Apollo-Simulation-Peripheral-Lab/DSKY/3D Models/iPhone 13 Version/Cover (iPhone 13).3mf

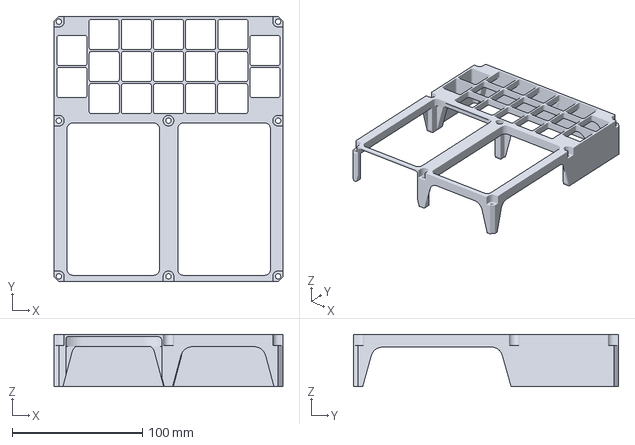
[picture p16: CAD file, 2024-06-18]
3D Models/iPhone 13 Version/Cover (iPhone 13).3mf
175.3 x 203.2 x 39.9 mm
