Apollo-Simulation-Peripheral-Lab/DSKY/3D Models/Common Models/Alarm Housing Top.stl

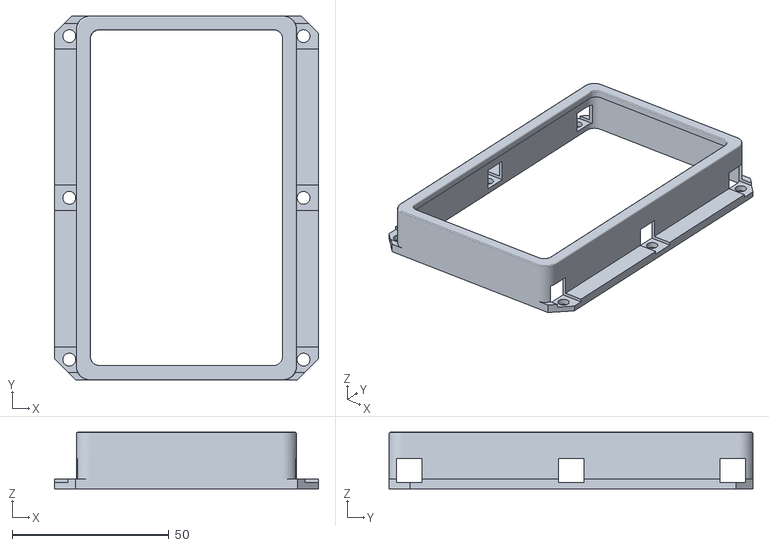
[picture p17: CAD file, 2024-06-30]
3D Models/Common Models/Alarm Housing Top.stl
84.2 x 116.1 x 18.0
