Apollo-Simulation-Peripheral-Lab/DSKY/3D Models/HDMI Version/Display Housing (HDMI).stl

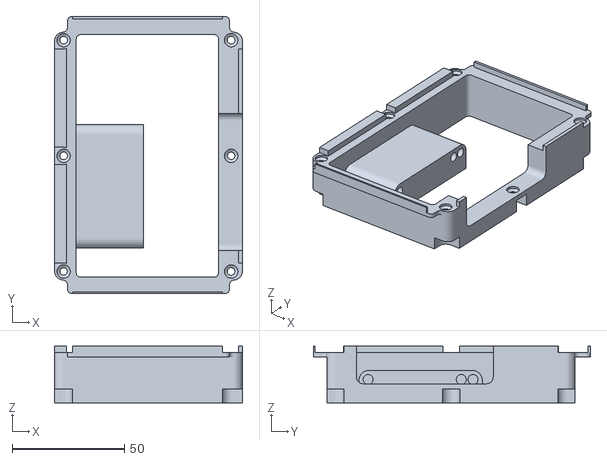
[picture p18: CAD file, 2024-06-30]
3D Models/HDMI Version/Display Housing (HDMI).stl
83.8 x 123.5 x 25.3
