Apollo-Simulation-Peripheral-Lab/DSKY/3D Models/iPhone 12 Mini Version/Frame (iPhone 12 Mini).3mf

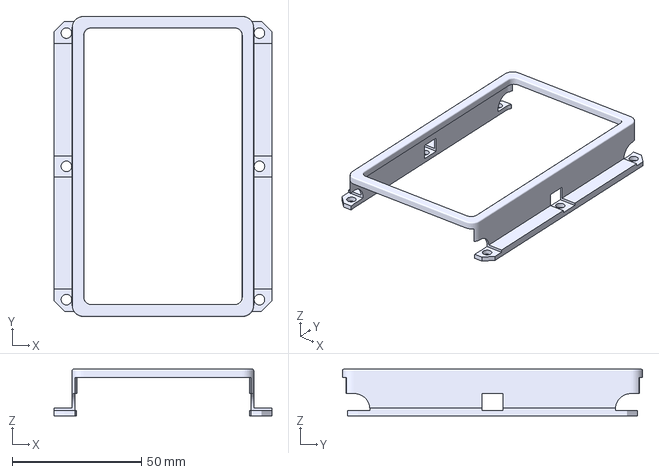
[picture p19: CAD file, 2024-06-18]
3D Models/iPhone 12 Mini Version/Frame (iPhone 12 Mini).3mf
84.2 x 116.1 x 18.0 mm
