Apollo-Simulation-Peripheral-Lab/DSKY/3D Models/Common Models/Keyboard Holder.stl

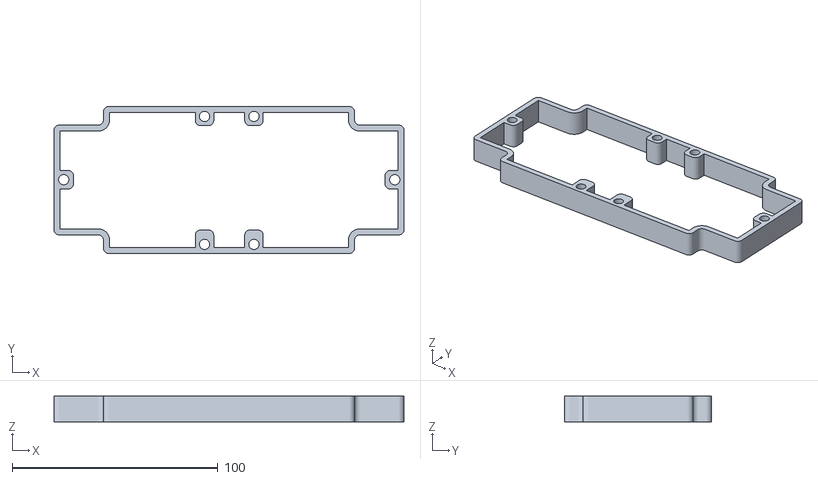
[picture p20: CAD file, 2024-06-30]
3D Models/Common Models/Keyboard Holder.stl
170.0 x 71.4 x 12.4
