Apollo-Simulation-Peripheral-Lab/DSKY/3D Models/HDMI Version/Compact Enclosure.stl

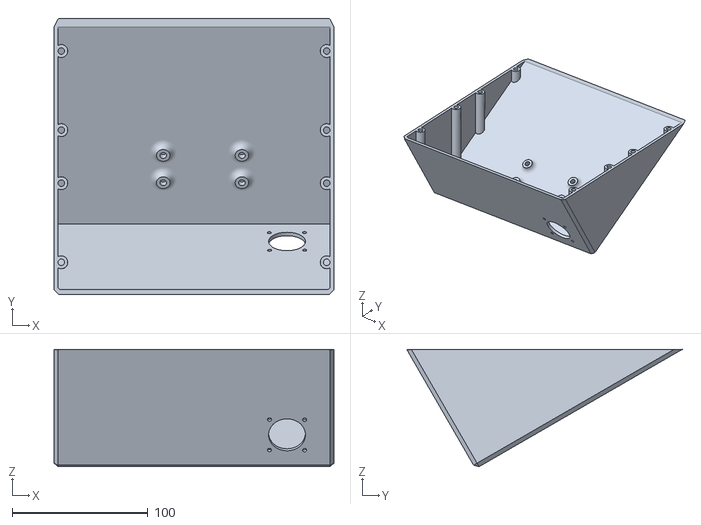
[picture p21: CAD file, 2024-06-30]
3D Models/HDMI Version/Compact Enclosure.stl
206.3 x 203.2 x 86.5
