Apollo-Simulation-Peripheral-Lab/DSKY/3D Models/Common Models/Alarm Housing Bottom.stl

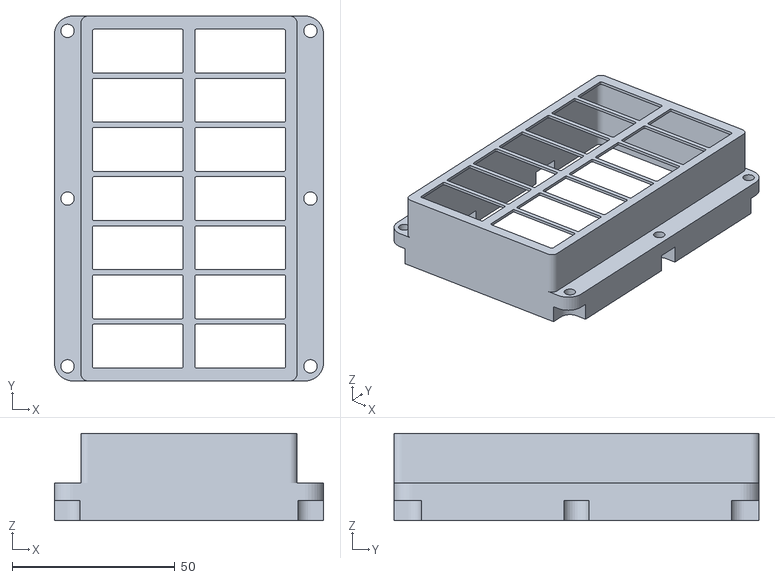
[picture p22: CAD file, 2024-06-30]
3D Models/Common Models/Alarm Housing Bottom.stl
82.8 x 112.2 x 26.9
