Apollo-Simulation-Peripheral-Lab/DSKY/3D Models/Common Models/Mount Top.stl

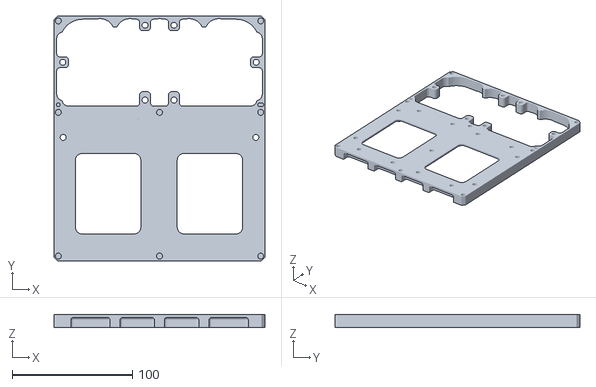
[picture p23: CAD file, 2024-06-18]
3D Models/Common Models/Mount Top.stl
175.3 x 203.2 x 10.9
