Apollo-Simulation-Peripheral-Lab/DSKY/3D Models/HDMI Version/Enclosure middle.3mf

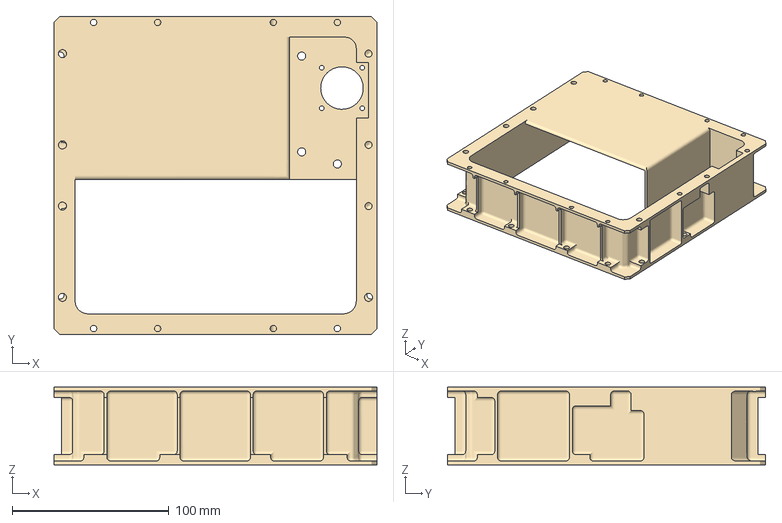
[picture p24: CAD file, 2024-04-06]
3D Models/HDMI Version/Enclosure middle.3mf
206.3 x 203.2 x 49.8 mm
