Apollo-Simulation-Peripheral-Lab/DSKY/3D Models/Common Models/Keys/KEY REL.stl

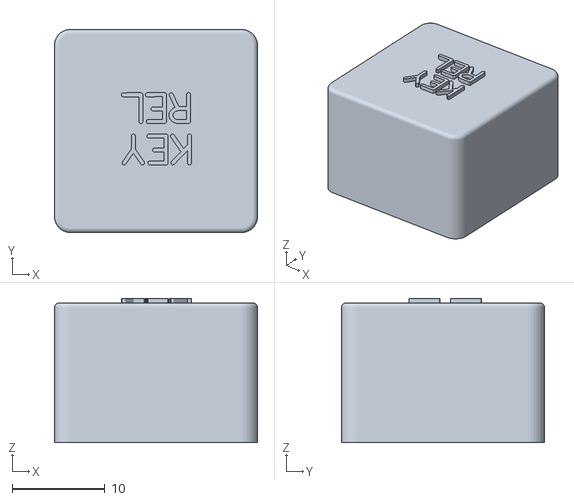
[picture p25: CAD file, 2024-06-18]
3D Models/Common Models/Keys/KEY REL.stl
21.8 x 21.8 x 15.5
