Apollo-Simulation-Peripheral-Lab/DSKY/3D Models/Common Models/Mount Bottom.stl

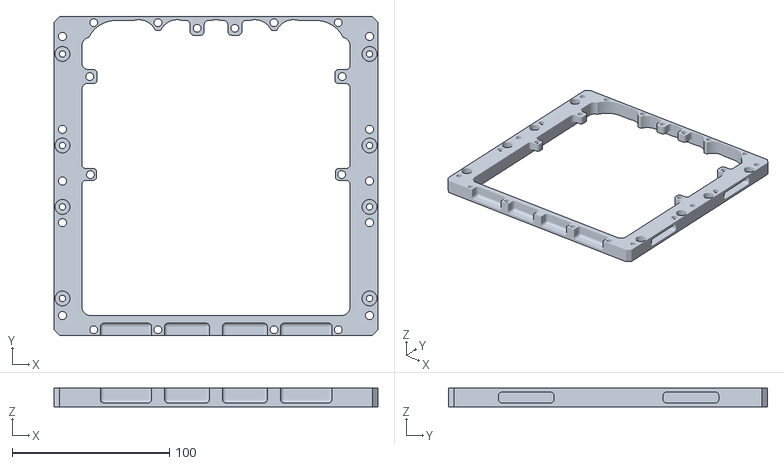
[picture p26: CAD file, 2024-06-18]
3D Models/Common Models/Mount Bottom.stl
206.3 x 203.2 x 12.0
