Apollo-Simulation-Peripheral-Lab/DSKY/3D Models/HDMI Version/Enclosure bottom.3mf

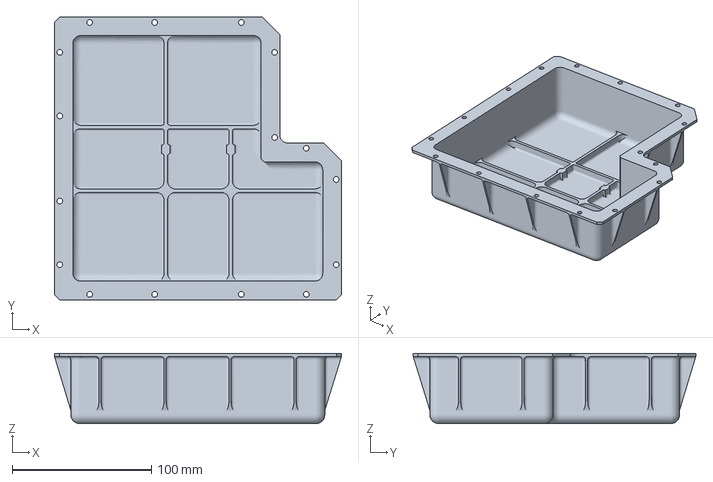
[picture p27: CAD file, 2024-02-14]
3D Models/HDMI Version/Enclosure bottom.3mf
206.3 x 203.2 x 50.4 mm
