Apollo-Simulation-Peripheral-Lab/DSKY/3D Models/Common Models/Enclosure middle (top half).3mf

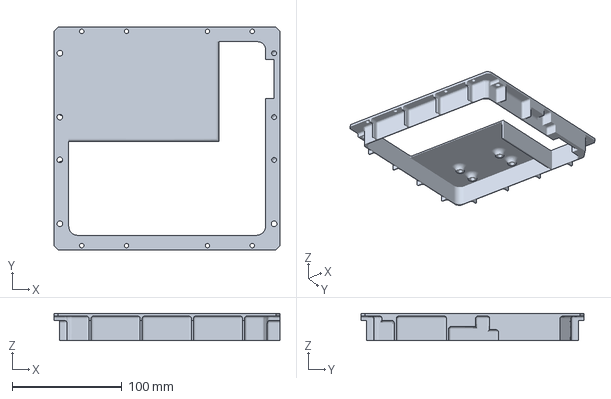
[picture p28: CAD file, 2024-06-18]
3D Models/Common Models/Enclosure middle (top half).3mf
206.3 x 203.2 x 25.0 mm
