Apollo-Simulation-Peripheral-Lab/DSKY/3D Models/Common Models/Alarm Splitter.3mf

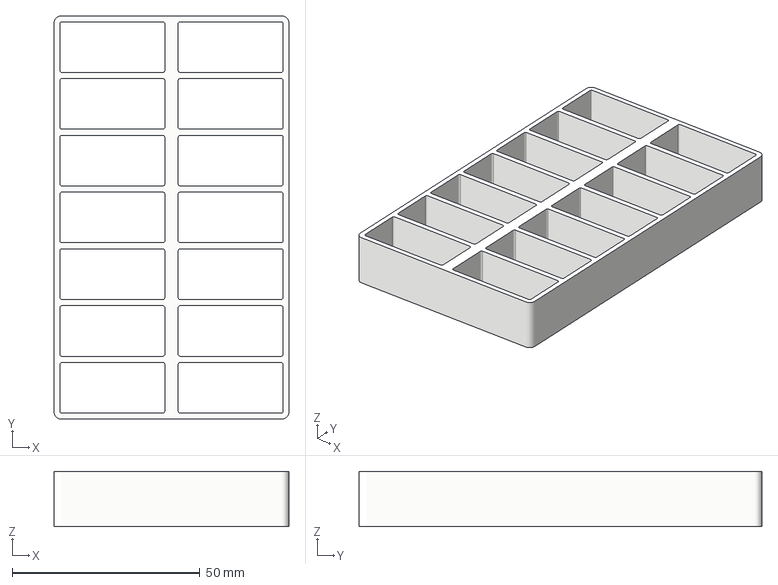
[picture p29: CAD file, 2024-06-18]
3D Models/Common Models/Alarm Splitter.3mf
62.5 x 107.3 x 14.7 mm
