Apollo-Simulation-Peripheral-Lab/DSKY/3D Models/Common Models/Enclosure middle (bottom half).3mf

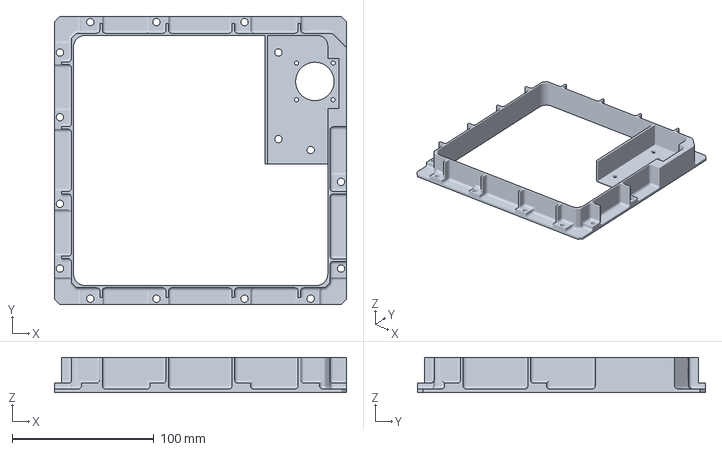
[picture p30: CAD file, 2024-06-18]
3D Models/Common Models/Enclosure middle (bottom half).3mf
206.3 x 203.2 x 24.8 mm
