Apollo-Simulation-Peripheral-Lab/DSKY/3D Models/Common Models/Mount (single print discouraged).3mf

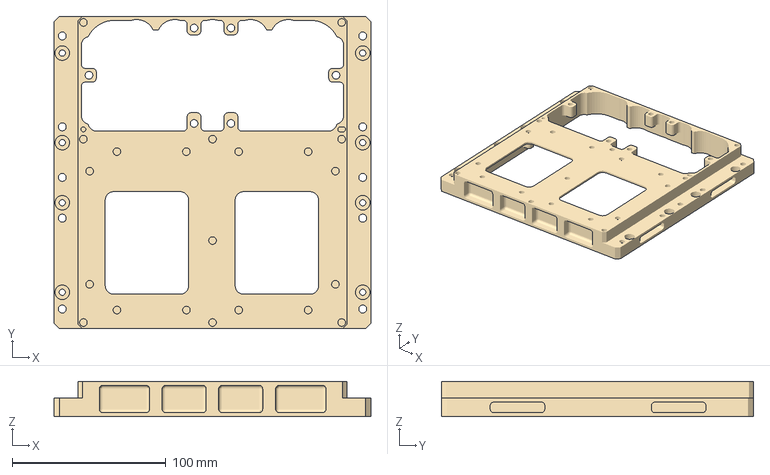
[picture p31: CAD file, 2024-04-12]
3D Models/Common Models/Mount (single print discouraged).3mf
206.3 x 203.2 x 22.9 mm
