Apollo-Simulation-Peripheral-Lab/DSKY/3D Models/Common Models/Alarm Holder 3x7mm.3mf

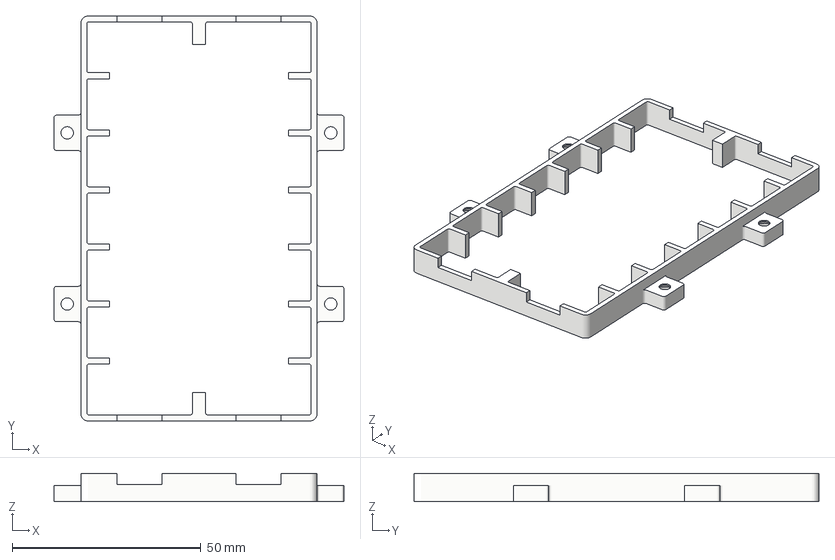
[picture p32: CAD file, 2024-03-08]
3D Models/Common Models/Alarm Holder 3x7mm.3mf
76.8 x 107.3 x 7.55 mm
