Apollo-Simulation-Peripheral-Lab/DSKY/firmware/template/src/main.h

#ifndef __main_h_
#define __main_h_
//////////////
/* Includes */

///////////////////
/* Public Macros */

//////////////////
/* Public Types */

/////////////////
/* Public Data */

////////////////////////////////
/* Public Function Prototypes */

#endif /* __main_h_ */
